chuckfletcherIV/DIYIOT-for-node-red/Firmware/mqtt_8266_pir_Board_E/mqtt_8266_pir/mqtt_8266_pir.ino

#include <ESP8266WiFi.h>
#include <PubSubClient.h>

const char* ssid     = "DIYIOT";
const char* password = "diyiotdiyiot";
const char* mqtt_server = "10.10.10.3";
const char* topic = "pir/1";
char msg[50];
char message_buffer[100];
String myMsg;

int calibrationTime = 15;        

//the time when the sensor outputs a low impulse
long unsigned int lowIn;         

//the amount of milliseconds the sensor has to be low 
//before we assume all motion has stopped
long unsigned int pause = 2000;  

boolean lockLow = true;
boolean takeLowTime;  

int pirPin = 13;    //the digital pin connected to the PIR sensor's output
int ledPin = 2;

WiFiClient espClient;
PubSubClient client(espClient);

/////////////////////////////
//SETUP
void setup(){
  setup_wifi();
  client.setServer(mqtt_server, 1883);
  client.setCallback(callback);
  Serial.begin(115200);
  pinMode(pirPin, INPUT);
  pinMode(ledPin, OUTPUT);
  digitalWrite(pirPin, LOW);

  //give the sensor some time to calibrate
  Serial.print("calibrating sensor ");
    for(int i = 0; i < calibrationTime; i++){
      Serial.print(".");
      delay(1000);
      }
    Serial.println(" done");
    Serial.println("SENSOR ACTIVE");
    delay(50);
  }


void setup_wifi() {

  delay(10);
  // We start by connecting to a WiFi network
  Serial.println();
  Serial.print("Connecting to ");
  Serial.println(ssid);

  WiFi.begin(ssid, password);

  while (WiFi.status() != WL_CONNECTED) {
    delay(500);
    Serial.print(".");
  }

  Serial.println("");
  Serial.println("WiFi connected");
  Serial.println("IP address: ");
  Serial.println(WiFi.localIP());
}


void callback(char* topic, byte* payload, unsigned int length) {
 int i = 0;
  Serial.print("Message arrived [");
  Serial.print(topic);
  Serial.print("] ");
  payload[length] = '\0';
}

void reconnect() {
  // Loop until we're reconnected
  while (!client.connected()) {
    
      Serial.print("Attempting MQTT connection...");
    // Attempt to connect
    if (client.connect(topic)) {
      Serial.println("Connected");
      // Once connected, publish an announcement...
      client.publish(topic, "connected");
      client.publish("channels", topic);
      // ... and resubscribe
      //client.subscribe(topic);
    } else {
      Serial.print("failed, rc=");
      Serial.print(client.state());
      Serial.println(" try again in 5 seconds");
      // Wait 5 seconds before retrying
      delay(5000);
    }
  }
}

////////////////////////////
//LOOP
void loop(){
  
      if (!client.connected()) {
      reconnect();
      }

      client.loop();   

     if(digitalRead(pirPin) == HIGH){
       digitalWrite(ledPin, HIGH);   //the led visualizes the sensors output pin state
       if(lockLow){  
         //makes sure we wait for a transition to LOW before any further output is made:
         lockLow = false;            
         Serial.println("---");
         Serial.print("motion detected at ");
         client.publish(topic, "motion");
         Serial.print(millis()/1000);
         Serial.println(" sec"); 
         delay(50);
         }         
         takeLowTime = true;
       }

     if(digitalRead(pirPin) == LOW){       
       digitalWrite(ledPin, LOW);  //the led visualizes the sensors output pin state

       if(takeLowTime){
        lowIn = millis();          //save the time of the transition from high to LOW
        takeLowTime = false;       //make sure this is only done at the start of a LOW phase
        }
       //if the sensor is low for more than the given pause, 
       //we assume that no more motion is going to happen
       if(!lockLow && millis() - lowIn > pause){  
           //makes sure this block of code is only executed again after 
           //a new motion sequence has been detected
           lockLow = true;                        
           Serial.print("motion ended at ");      //output
           client.publish(topic, "no motion");
           Serial.print((millis() - pause)/1000);
           Serial.println(" sec");
           delay(50);
           }
       }
  }
