chuckfletcherIV/DIYIOT-for-node-red/Firmware/mqtt_8266_temp_and_humidity_sensor_Board_B/mqtt_8266_temp_and_humidity_sensor/mqtt_8266_temp_and_humidity_sensor.ino

// Example testing sketch for various DHT humidity/temperature sensors
// Written by ladyada, public domain
#include <ESP8266WiFi.h>
#include <PubSubClient.h>

const char* ssid     = "DIYIOT";
const char* password = "diyiotdiyiot";
const char* mqtt_server = "10.10.10.3";
const char* topic = "temp_humidity/1";
char msg[75];

#include "DHT.h"

#define DHTPIN 13     // what digital pin we're connected to

// Uncomment whatever type you're using!
#define DHTTYPE DHT11   // DHT 11
//#define DHTTYPE DHT22   // DHT 22  (AM2302), AM2321
//#define DHTTYPE DHT21   // DHT 21 (AM2301)

// Connect pin 1 (on the left) of the sensor to +5V
// NOTE: If using a board with 3.3V logic like an Arduino Due connect pin 1
// to 3.3V instead of 5V!
// Connect pin 2 of the sensor to whatever your DHTPIN is
// Connect pin 4 (on the right) of the sensor to GROUND
// Connect a 10K resistor from pin 2 (data) to pin 1 (power) of the sensor

// Initialize DHT sensor.
// Note that older versions of this library took an optional third parameter to
// tweak the timings for faster processors.  This parameter is no longer needed
// as the current DHT reading algorithm adjusts itself to work on faster procs.
DHT dht(DHTPIN, DHTTYPE);

WiFiClient espClient;
PubSubClient client(espClient);

/////////////////////////////

void setup() {
  Serial.begin(115200);
  setup_wifi();
  client.setServer(mqtt_server, 1883);
  client.setCallback(callback);
  dht.begin();
}

void setup_wifi() {

  delay(10);
  // We start by connecting to a WiFi network
  Serial.println();
  Serial.print("Connecting to ");
  Serial.println(ssid);

  WiFi.begin(ssid, password);

  while (WiFi.status() != WL_CONNECTED) {
    delay(500);
    Serial.print(".");
  }

  Serial.println("");
  Serial.println("WiFi connected");
  Serial.println("IP address: ");
  Serial.println(WiFi.localIP());
}


void callback(char* topic, byte* payload, unsigned int length) {
}

void reconnect() {
  // Loop until we're reconnected
  while (!client.connected()) {
    
      Serial.print("Attempting MQTT connection...");
    // Attempt to connect
    if (client.connect(topic)) {
      Serial.println("Connected");
      // Once connected, publish an announcement...
      client.publish("channels", topic);
      client.publish(topic, "connected");
      // ... and resubscribe
      //client.subscribe(topic);
    } else {
      Serial.print("failed, rc=");
      Serial.print(client.state());
      Serial.println(" try again in 5 seconds");
      // Wait 5 seconds before retrying
      delay(5000);
    }
  }
}

////////////////////////////
//LOOP
void loop(){
  
      if (!client.connected()) {
      reconnect();
      }

      client.loop();   

    
      // Wait a few seconds between measurements.
  delay(2000);

  // Reading temperature or humidity takes about 250 milliseconds!
  // Sensor readings may also be up to 2 seconds 'old' (its a very slow sensor)
  float h = dht.readHumidity();
  // Read temperature as Celsius (the default)
  float t = dht.readTemperature();
  // Read temperature as Fahrenheit (isFahrenheit = true)
  float f = dht.readTemperature(true);

  // Check if any reads failed and exit early (to try again).
  if (isnan(h) || isnan(t) || isnan(f)) {
    Serial.println("Failed to read from DHT sensor!");
    return;
  }

  // Compute heat index in Fahrenheit (the default)
  float hif = dht.computeHeatIndex(f, h);
  // Compute heat index in Celsius (isFahreheit = false)
  float hic = dht.computeHeatIndex(t, h, false);
  
  String tempHumidityString = String(h) + "," + String(f) + "," + String(hif);

  Serial.print("Humidity: ");
  Serial.print(h);
  Serial.print(" %\t");
  Serial.print("Temperature: ");
  Serial.print(t);
  Serial.print(" *C ");
  Serial.print(f);
  Serial.print(" *F\t");
  Serial.print("Heat index: ");
  Serial.print(hic);
  Serial.print(" *C ");
  Serial.print(hif);
  Serial.println(" *F");
  
  tempHumidityString.toCharArray(msg,75);
  client.publish(topic, msg);

  }
